stanislawq/Heart-Shaped-LED-PCB/Heart-Shaped-LED-PCB/images/3D_Model_Top.png

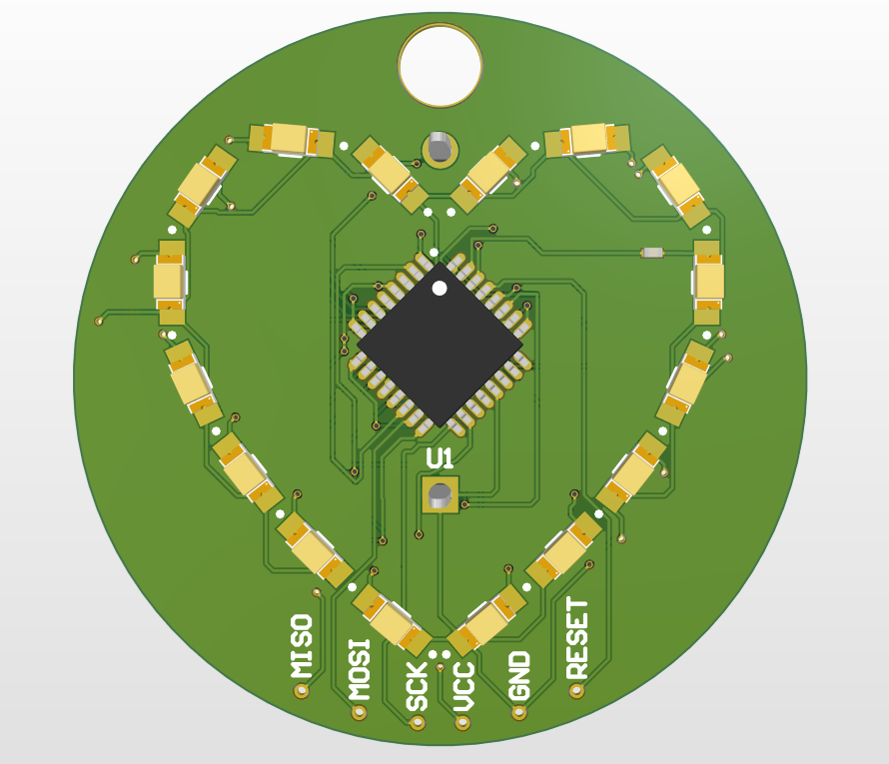
Heart-Shaped-LED-PCB/images/3D_Model_Top.png
