stanislawq/Heart-Shaped-LED-PCB/Heart-Shaped-LED-PCB/images/bare_pcb_front.jpg

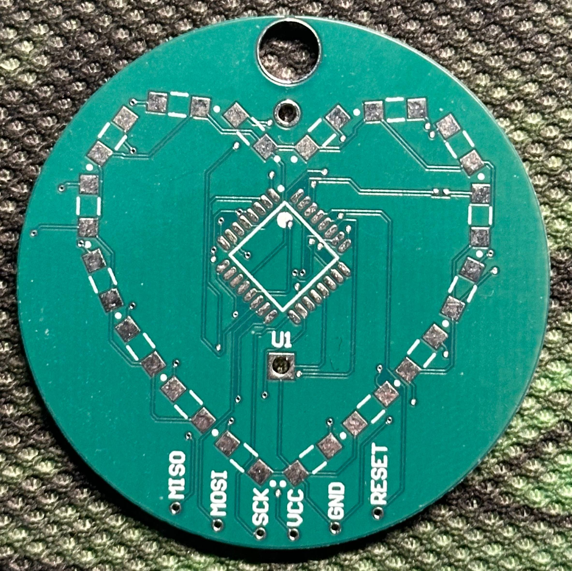
Heart-Shaped-LED-PCB/images/bare_pcb_front.jpg
